hayleymcclintock/project_cuboid/ROS_ws/src/control/master_controller/data/finger_a1/pics/1542583935.png

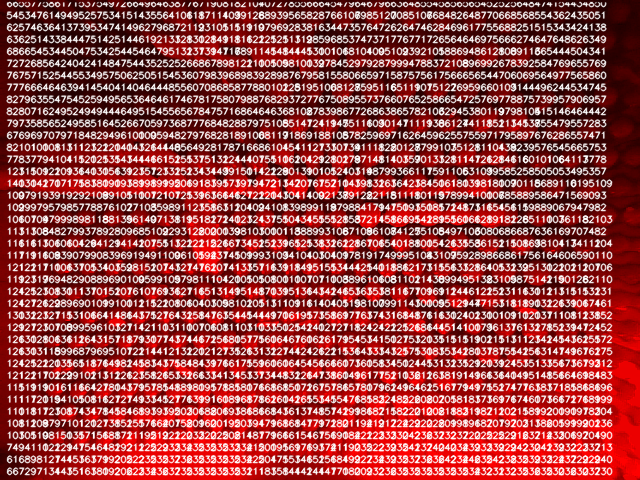
ROS_ws/src/control/master_controller/data/finger_a1/pics/1542583935.png
