hayleymcclintock/project_cuboid/ROS_ws/src/control/master_controller/data/finger_a2/pics/1542583973.png

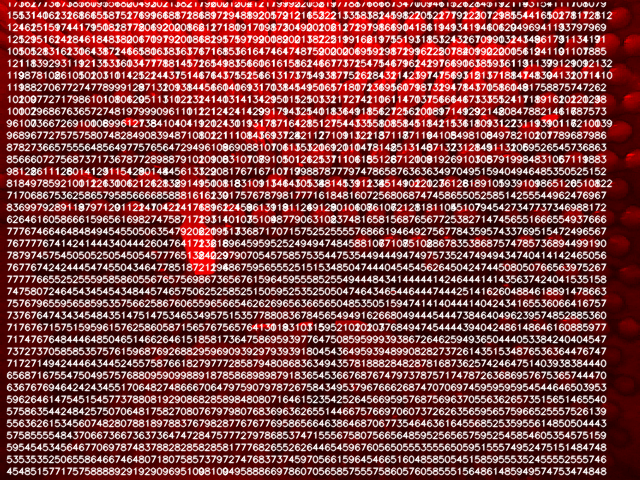
ROS_ws/src/control/master_controller/data/finger_a2/pics/1542583973.png
