hayleymcclintock/project_cuboid/ROS_ws/src/control/master_controller/data/finger_d1/pics/1542583783.png

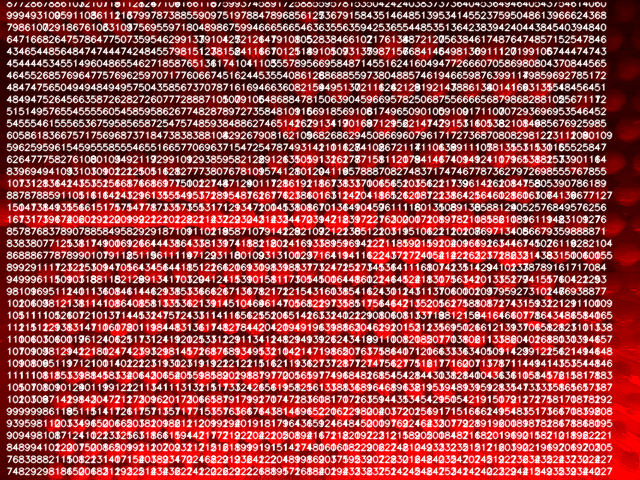
ROS_ws/src/control/master_controller/data/finger_d1/pics/1542583783.png
