hayleymcclintock/project_cuboid/ROS_ws/src/control/master_controller/data/finger_d2/pics/1542583851.png

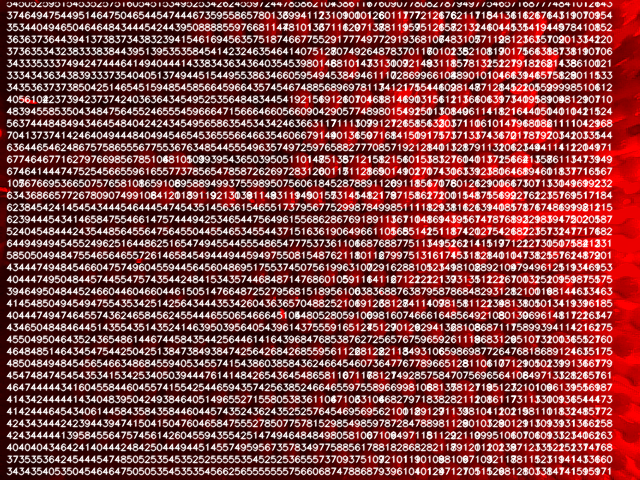
ROS_ws/src/control/master_controller/data/finger_d2/pics/1542583851.png
