hayleymcclintock/project_cuboid/ROS_ws/src/control/master_controller/data/nut_a1/pics/1542584776.png

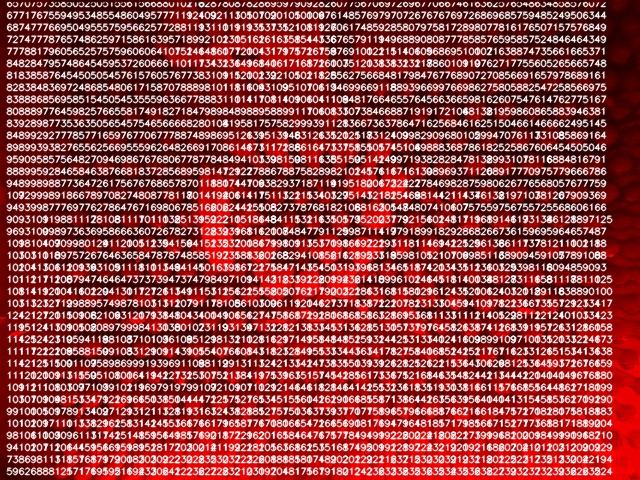
ROS_ws/src/control/master_controller/data/nut_a1/pics/1542584776.png
