hayleymcclintock/project_cuboid/ROS_ws/src/control/master_controller/data/nut_a2/pics/1542584799.png

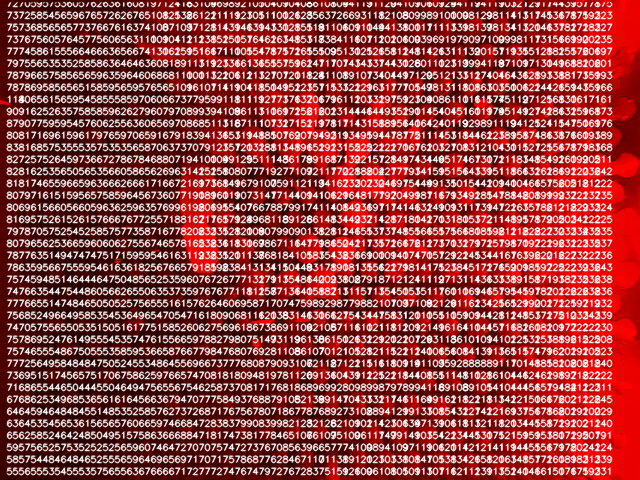
ROS_ws/src/control/master_controller/data/nut_a2/pics/1542584799.png
