hayleymcclintock/project_cuboid/ROS_ws/src/control/master_controller/data/nut_a2/pics/1542584809.png

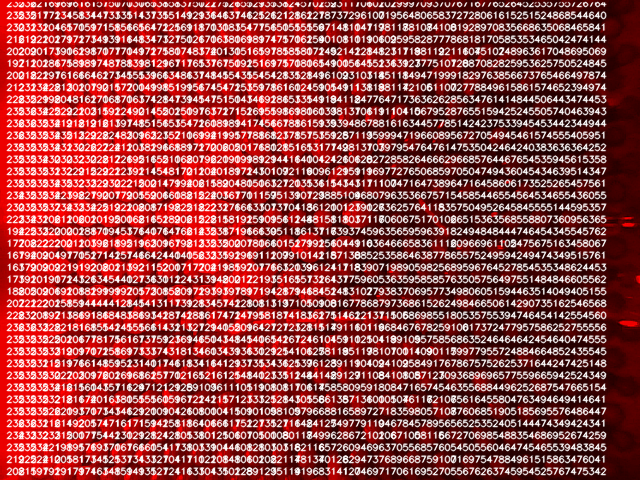
ROS_ws/src/control/master_controller/data/nut_a2/pics/1542584809.png
