hayleymcclintock/project_cuboid/ROS_ws/src/control/master_controller/data/nut_d1/pics/1542584872.png

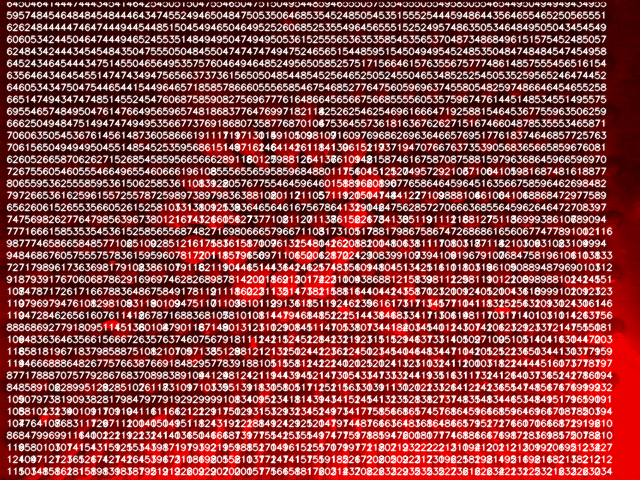
ROS_ws/src/control/master_controller/data/nut_d1/pics/1542584872.png
