hayleymcclintock/project_cuboid/ROS_ws/src/control/master_controller/data/nut_d2/pics/1542584908.png

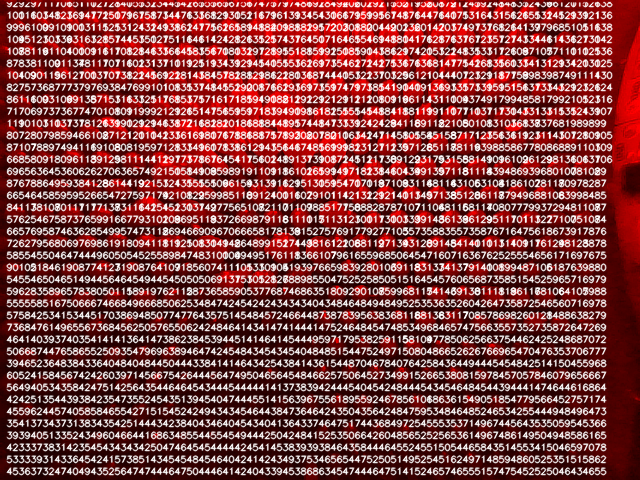
ROS_ws/src/control/master_controller/data/nut_d2/pics/1542584908.png
