hayleymcclintock/project_cuboid/ROS_ws/src/control/master_controller/data/rect_a1/pics/1542584318.png

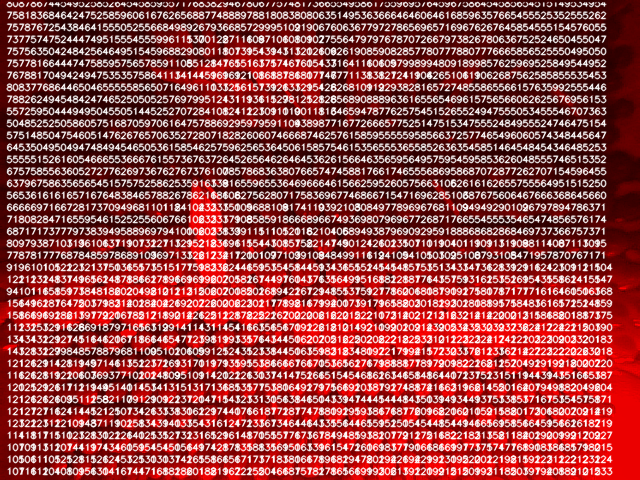
ROS_ws/src/control/master_controller/data/rect_a1/pics/1542584318.png
