hayleymcclintock/project_cuboid/ROS_ws/src/control/master_controller/data/rect_a2/pics/1542584374.png

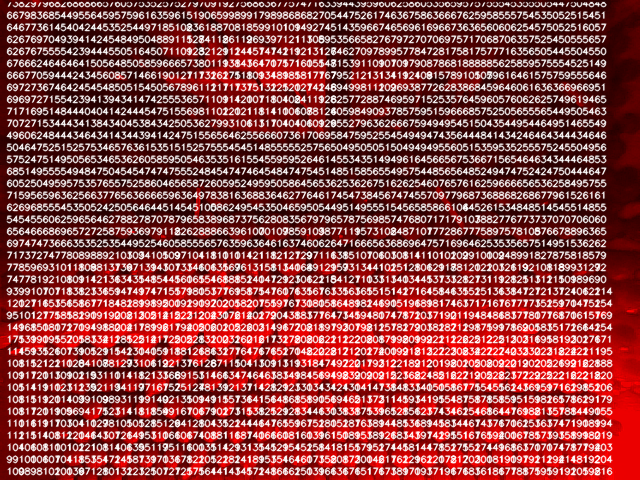
ROS_ws/src/control/master_controller/data/rect_a2/pics/1542584374.png
