hayleymcclintock/project_cuboid/ROS_ws/src/control/master_controller/data/rect_d1/pics/1542584445.png

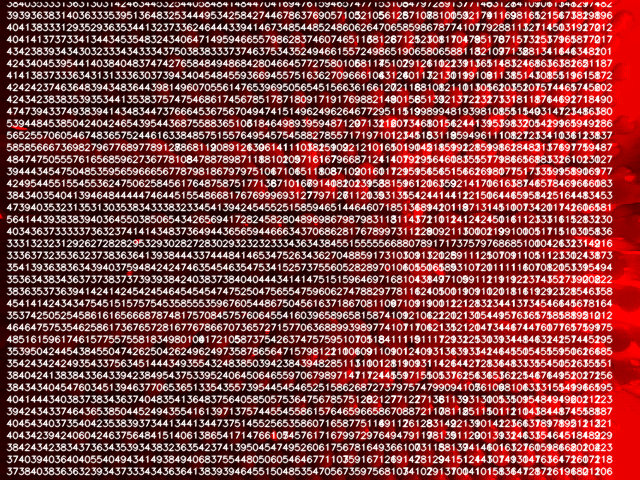
ROS_ws/src/control/master_controller/data/rect_d1/pics/1542584445.png
