hayleymcclintock/project_cuboid/ROS_ws/src/control/master_controller/data/rect_d1/pics/1542584450.png

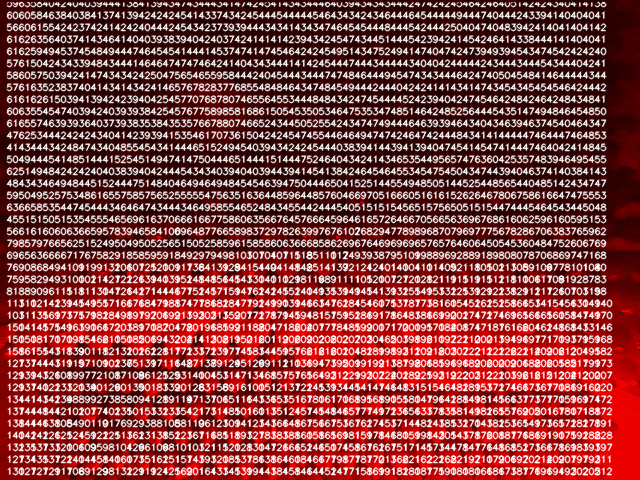
ROS_ws/src/control/master_controller/data/rect_d1/pics/1542584450.png
