hayleymcclintock/project_cuboid/ROS_ws/src/control/master_controller/data/rect_d2/pics/1542584489.png

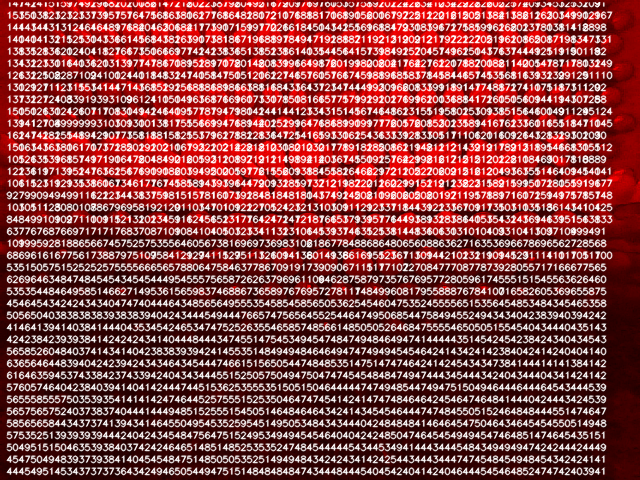
ROS_ws/src/control/master_controller/data/rect_d2/pics/1542584489.png
