hayleymcclintock/project_cuboid/ROS_ws/src/control/master_controller/data/tape_a1/pics/1542584672.png

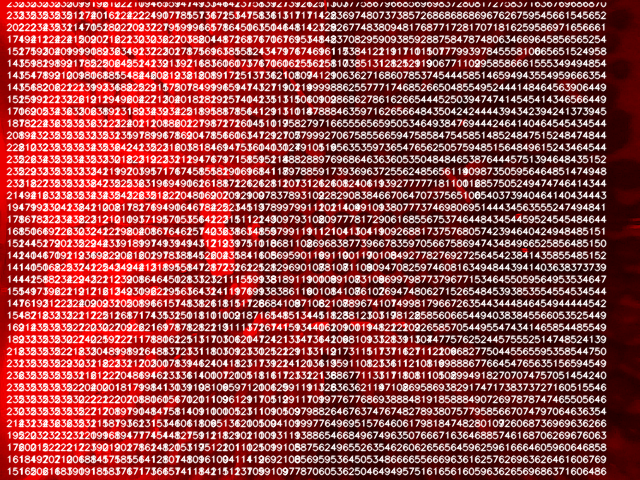
ROS_ws/src/control/master_controller/data/tape_a1/pics/1542584672.png
