hayleymcclintock/project_cuboid/ROS_ws/src/control/master_controller/data/tape_a2/pics/1542584689.png

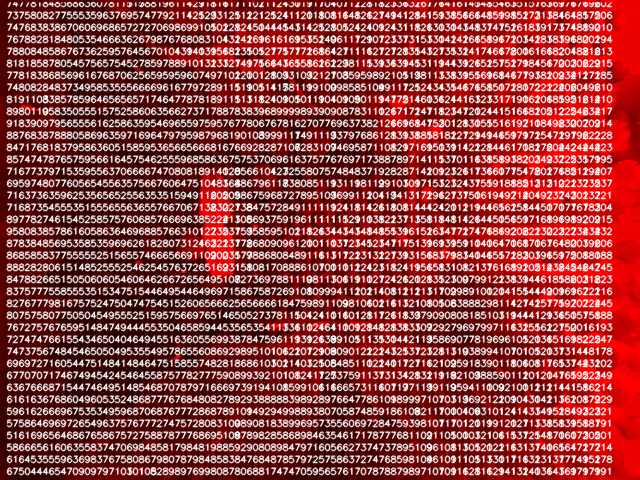
ROS_ws/src/control/master_controller/data/tape_a2/pics/1542584689.png
