hayleymcclintock/project_cuboid/ROS_ws/src/control/master_controller/data/tape_d1/pics/1542584591.png

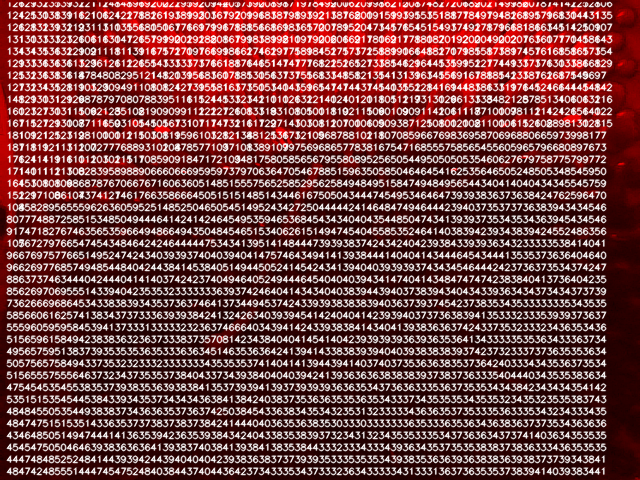
ROS_ws/src/control/master_controller/data/tape_d1/pics/1542584591.png
