hayleymcclintock/project_cuboid/ROS_ws/src/control/master_controller/data/tape_d2/pics/1542584604.png

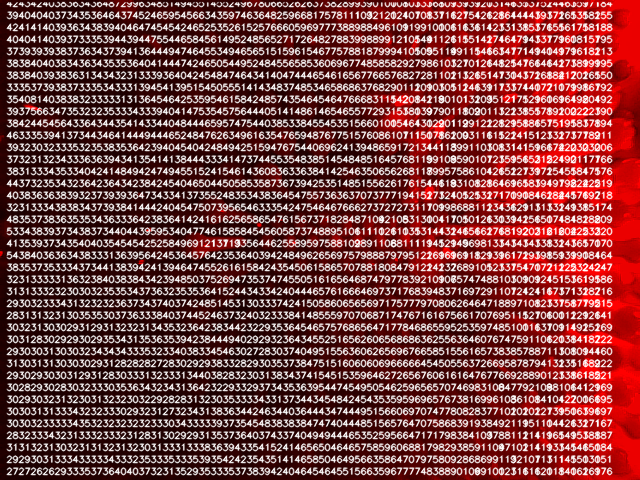
ROS_ws/src/control/master_controller/data/tape_d2/pics/1542584604.png
