hayleymcclintock/project_cuboid/Supplements/Presentations/1 First Checkin/First_attempt_surfaceMap.png

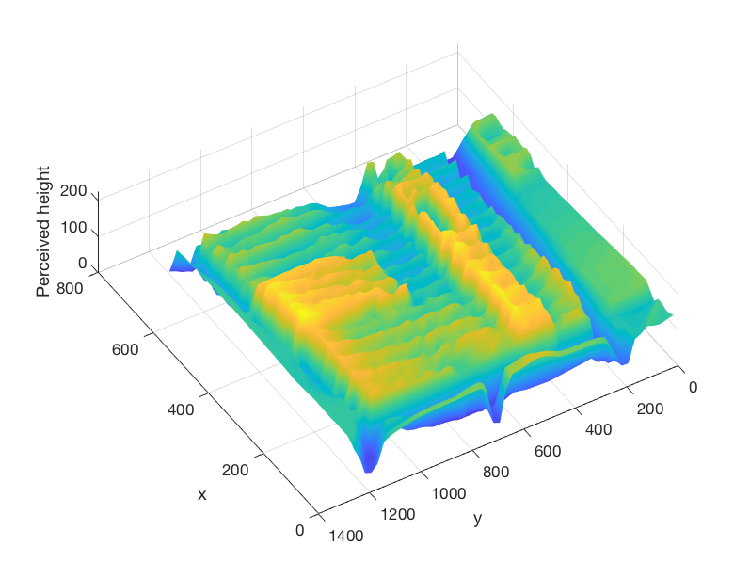
Supplements/Presentations/1 First Checkin/First_attempt_surfaceMap.png
