hayleymcclintock/project_cuboid/Supplements/Presentations/2 Second Checkin/2 Connected Solenoids/Capture.PNG

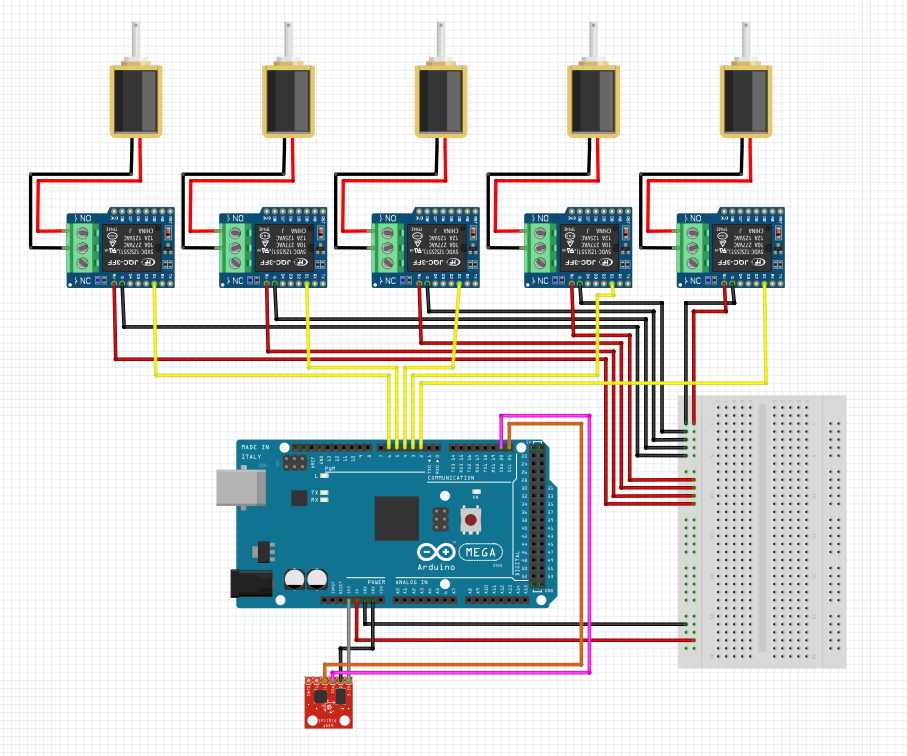
Supplements/Presentations/2 Second Checkin/2 Connected Solenoids/Capture.PNG
