hayleymcclintock/project_cuboid/Supplements/Parts/CAD/bracket.SLDPRT

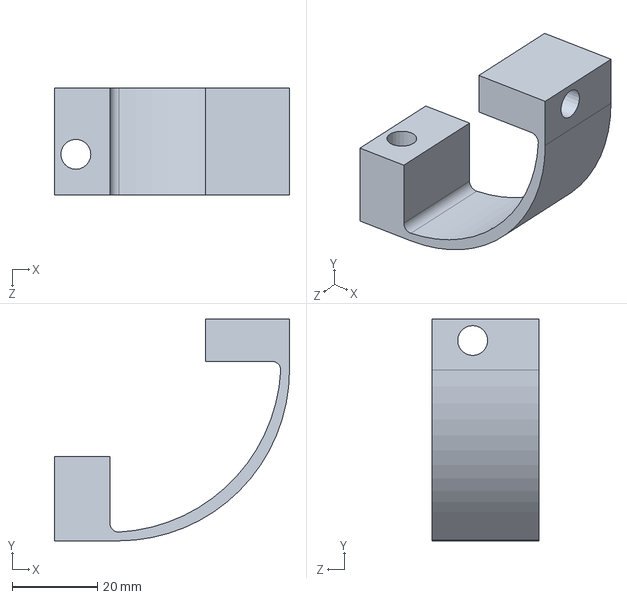
[picture p90: CAD file, 2018-11-29]
Supplements/Parts/CAD/bracket.SLDPRT
55.0 x 51.9 x 25.0 mm
