hayleymcclintock/project_cuboid/Supplements/Parts/CAD/spacer cap.SLDPRT

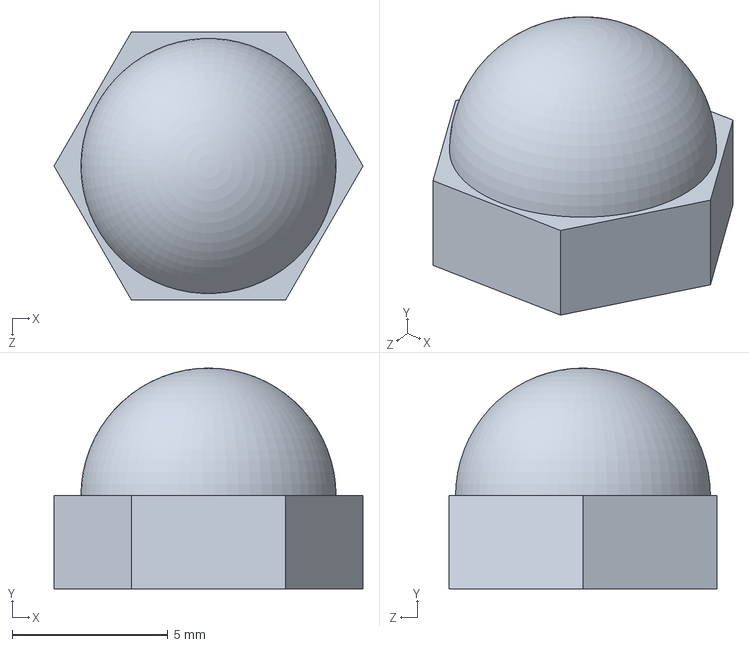
[picture p91: CAD file, 2018-11-29]
Supplements/Parts/CAD/spacer cap.SLDPRT
9.93 x 7.10 x 8.60 mm
