hayleymcclintock/project_cuboid/Supplements/Parts/CAD/director.SLDPRT

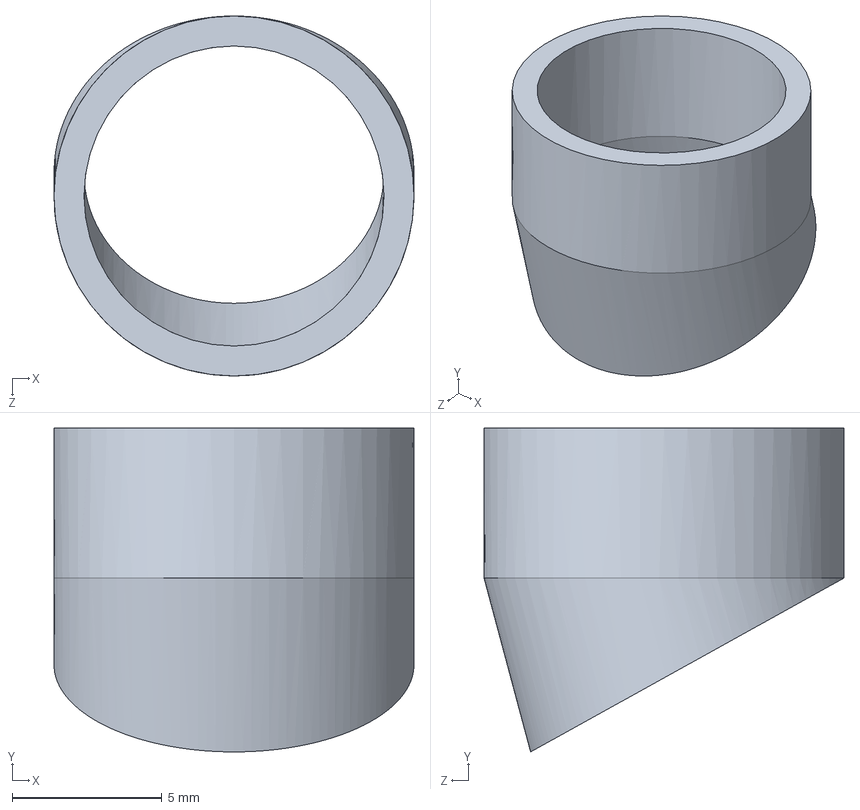
[picture p92: CAD file, 2018-11-29]
Supplements/Parts/CAD/director.SLDPRT
12.0 x 10.8 x 12.0 mm
