hayleymcclintock/project_cuboid/Supplements/Parts/CAD/spacer2.SLDPRT

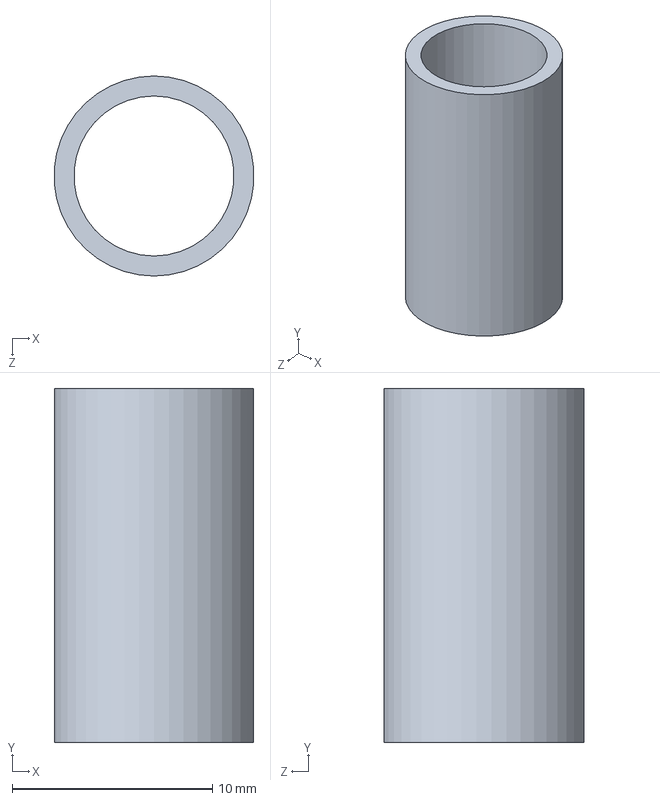
[picture p93: CAD file, 2018-11-29]
Supplements/Parts/CAD/spacer2.SLDPRT
9.97 x 17.7 x 10.0 mm
