hayleymcclintock/project_cuboid/Supplements/Parts/CAD/camera_mount.SLDPRT

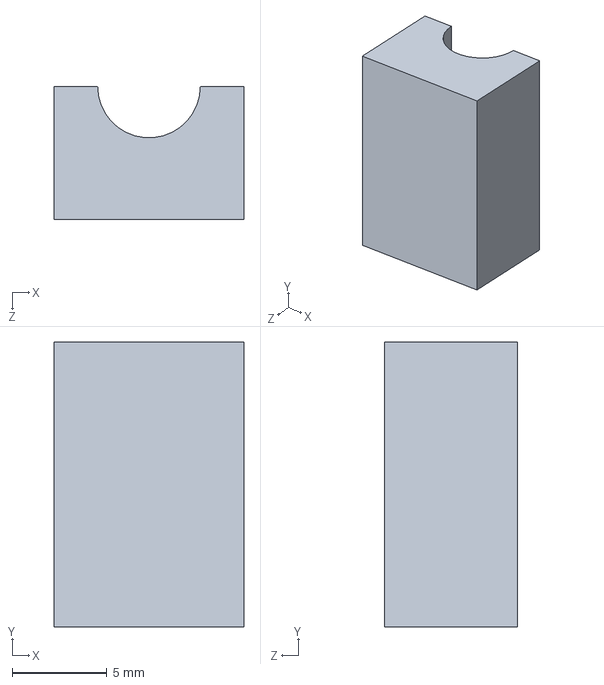
[picture p94: CAD file, 2018-11-29]
Supplements/Parts/CAD/camera_mount.SLDPRT
10.0 x 15.0 x 7.00 mm
