hayleymcclintock/project_cuboid/Supplements/Parts/CAD/dowel.SLDPRT

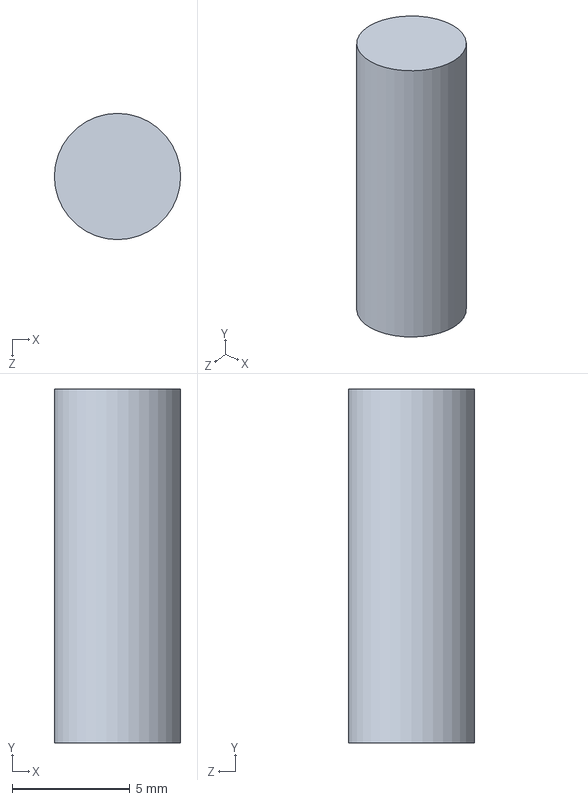
[picture p95: CAD file, 2018-11-29]
Supplements/Parts/CAD/dowel.SLDPRT
5.35 x 15.0 x 5.35 mm
