hayleymcclintock/project_cuboid/Supplements/Parts/CAD/trimmed side.SLDPRT

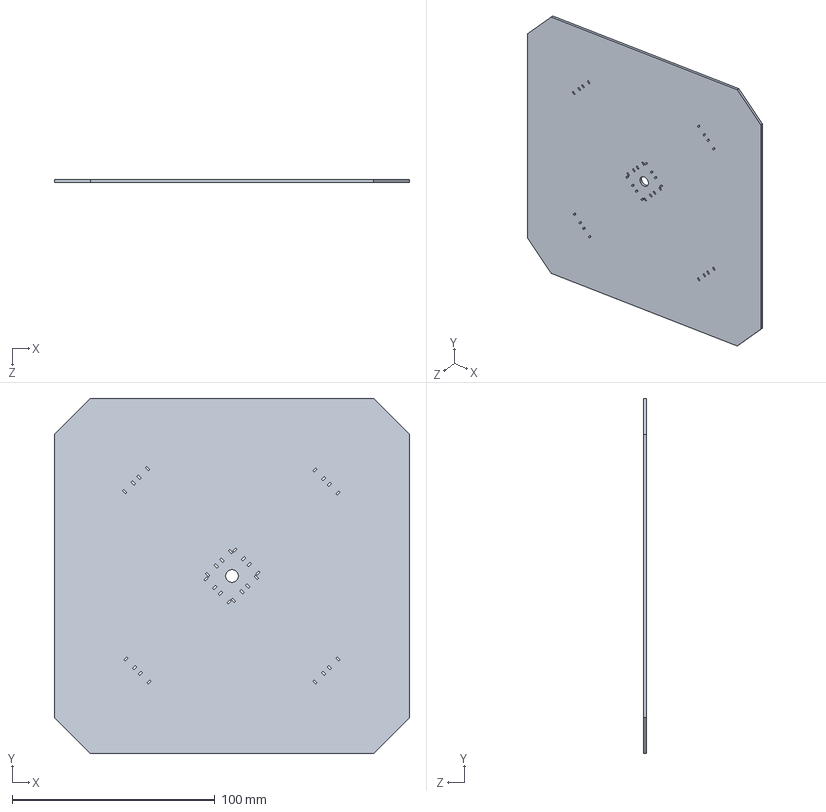
[picture p96: CAD file, 2018-11-29]
Supplements/Parts/CAD/trimmed side.SLDPRT
175.0 x 175.0 x 1.59 mm
