hayleymcclintock/project_cuboid/ROS_ws/src/hardware_coms/Arduino Code/Tests/Test_LED/Test_LED.ino

// script written by rob 11/5 to test the capacities of the LED

#include "FastLED.h"

// how much power are we going to draw? we have 30 led/meter. and 1 meter. 
// we power at 5v, and 

 
// How many leds in your strip?
#define NUM_LEDS 60
 
#define DATA_PIN 6
#define CLOCK_PIN 7
 
CRGB leds[NUM_LEDS]; // set up block of memory used for storing and manipulating LED data 


// code adapted from https://www.norwegiancreations.com/2018/01/programming-digital-rgb-led-strips-with-arduino-and-the-fastled-library/
 
void setup() { 
    // Uncomment/edit one of the following lines for your leds arrangement.
    // FastLED.addLeds<TM1803, DATA_PIN, RGB>(leds, NUM_LEDS);
    // FastLED.addLeds<TM1804, DATA_PIN, RGB>(leds, NUM_LEDS);
    // FastLED.addLeds<TM1809, DATA_PIN, RGB>(leds, NUM_LEDS);
    // FastLED.addLeds<WS2811, DATA_PIN, RGB>(leds, NUM_LEDS);
    // FastLED.addLeds<WS2812, DATA_PIN, RGB>(leds, NUM_LEDS);
    // FastLED.addLeds<WS2812B, DATA_PIN, RGB>(leds, NUM_LEDS);
    // FastLED.addLeds<NEOPIXEL, DATA_PIN>(leds, NUM_LEDS);
    // FastLED.addLeds<APA104, DATA_PIN, RGB>(leds, NUM_LEDS);
    // FastLED.addLeds<UCS1903, DATA_PIN, RGB>(leds, NUM_LEDS);
    // FastLED.addLeds<UCS1903B, DATA_PIN, RGB>(leds, NUM_LEDS);
    // FastLED.addLeds<GW6205, DATA_PIN, RGB>(leds, NUM_LEDS);
    // FastLED.addLeds<GW6205_400, DATA_PIN, RGB>(leds, NUM_LEDS);
 
    // FastLED.addLeds<WS2801, RGB>(leds, NUM_LEDS);
    // FastLED.addLeds<SM16716, RGB>(leds, NUM_LEDS);
    // FastLED.addLeds<LPD8806, RGB>(leds, NUM_LEDS);
    // FastLED.addLeds<P9813, RGB>(leds, NUM_LEDS);
    // FastLED.addLeds<APA102, RGB>(leds, NUM_LEDS);
    // FastLED.addLeds<DOTSTAR, RGB>(leds, NUM_LEDS);
 
     FastLED.addLeds<WS2801, DATA_PIN, CLOCK_PIN, RGB>(leds, NUM_LEDS);
    // FastLED.addLeds<SM16716, DATA_PIN, CLOCK_PIN, RGB>(leds, NUM_LEDS);
    // FastLED.addLeds<LPD8806, DATA_PIN, CLOCK_PIN, RGB>(leds, NUM_LEDS);
    // FastLED.addLeds<P9813, DATA_PIN, CLOCK_PIN, RGB>(leds, NUM_LEDS);
    // FastLED.addLeds<APA102, DATA_PIN, CLOCK_PIN, RGB>(leds, NUM_LEDS);
    // FastLED.addLeds<DOTSTAR, DATA_PIN, CLOCK_PIN, RGB>(leds, NUM_LEDS);
}
 
void loop() {
    for(int i=0; i<NUM_LEDS; i++){
        leds[i] = CHSV(160, 255, 128);
        FastLED.show();
        delay(50);
        leds[i] = CHSV(0,0,0);        FastLED.show();
    }




}
